raspberrypilearning/astro-pi-flight-case-mk2/en/images/all_4_spacers.jpg

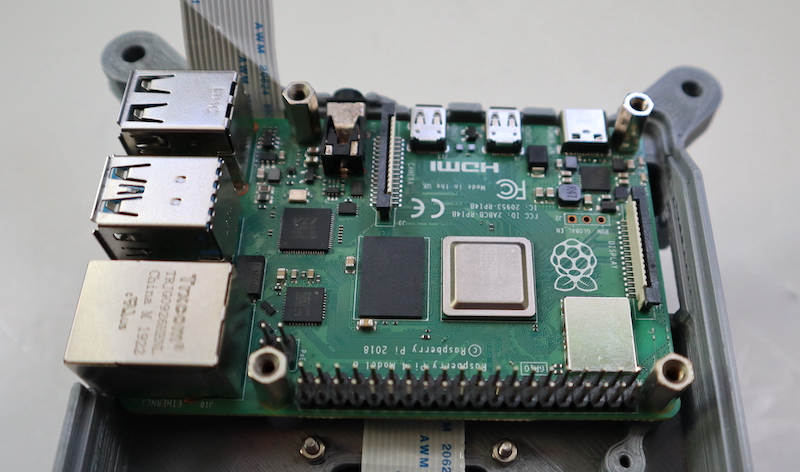
en/images/all_4_spacers.jpg
