raspberrypilearning/astro-pi-flight-case-mk2/en/images/both_panels.jpg

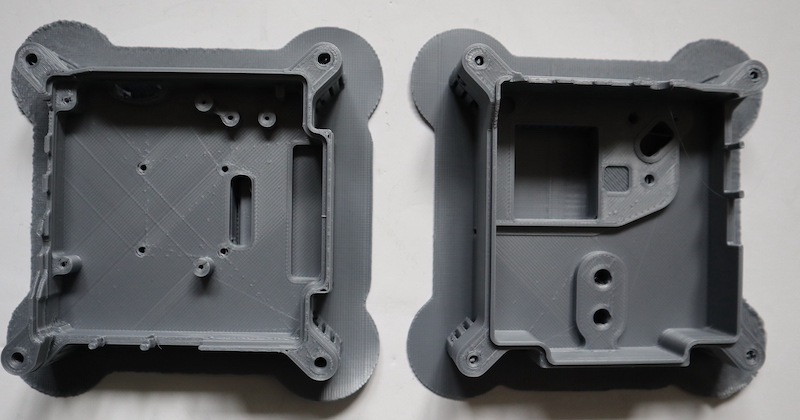
en/images/both_panels.jpg
