raspberrypilearning/astro-pi-flight-case-mk2/en/images/buttons_heatgun.JPG

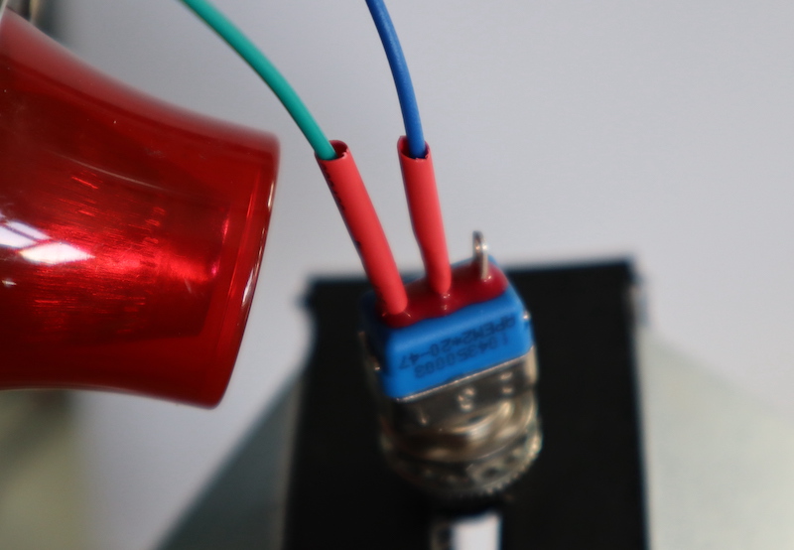
en/images/buttons_heatgun.JPG
