raspberrypilearning/astro-pi-flight-case-mk2/en/images/camera-slot-removed.jpg

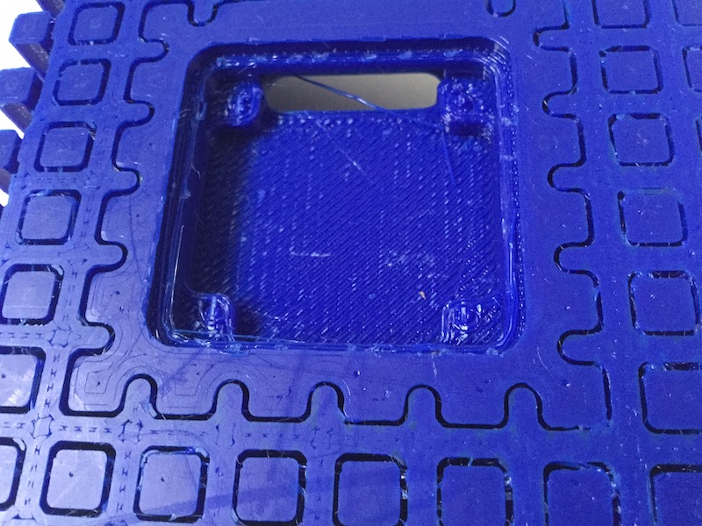
en/images/camera-slot-removed.jpg
