raspberrypilearning/astro-pi-flight-case-mk2/en/images/camera_mount_with_HQC_back.JPG

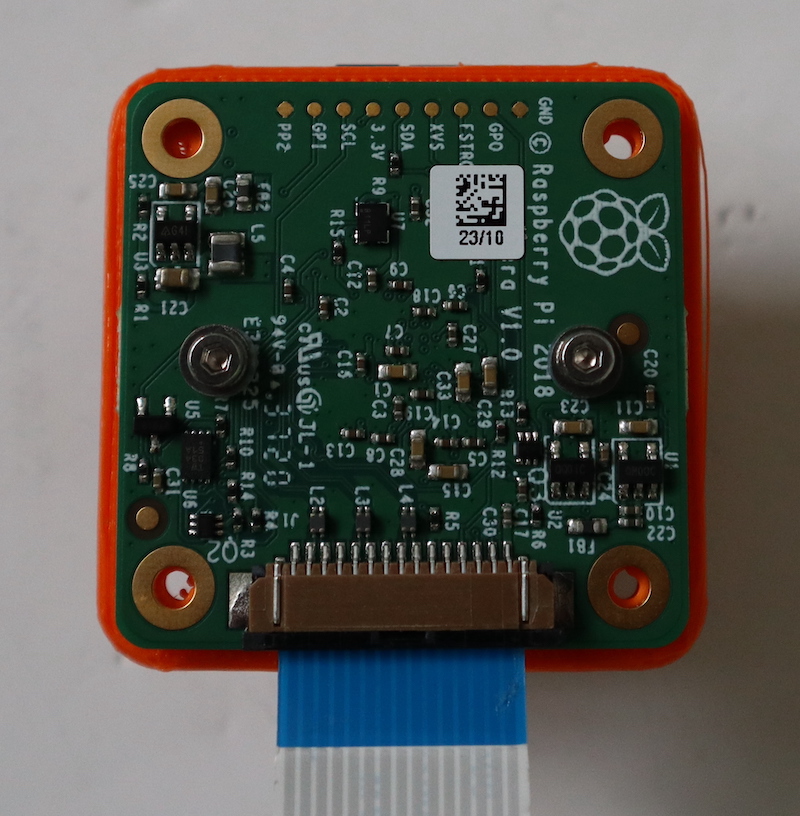
en/images/camera_mount_with_HQC_back.JPG
