raspberrypilearning/astro-pi-flight-case-mk2/en/images/completed_k.jpg

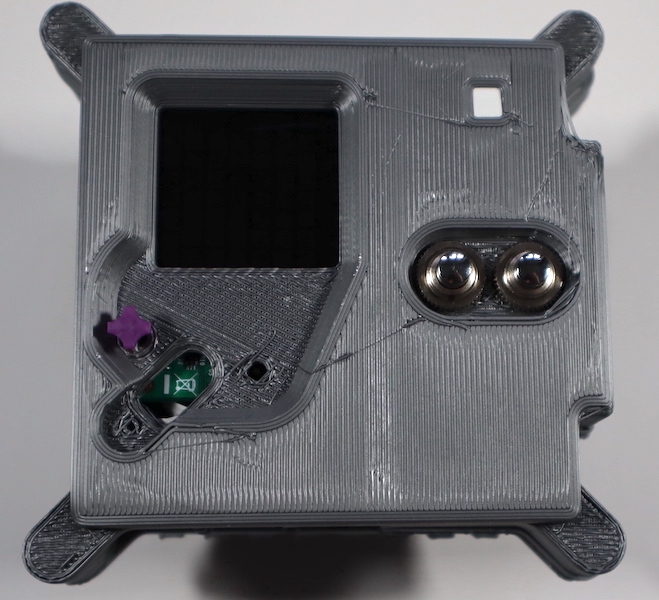
en/images/completed_k.jpg
