raspberrypilearning/astro-pi-flight-case-mk2/en/images/completed_p.jpg

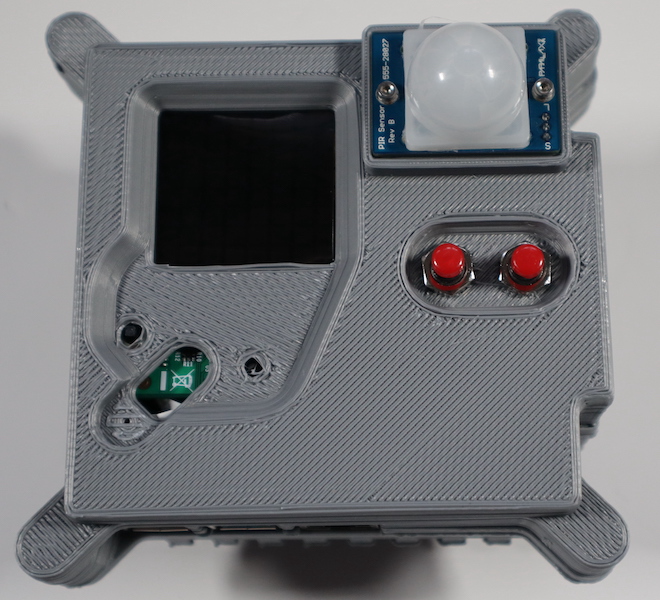
en/images/completed_p.jpg
