raspberrypilearning/astro-pi-flight-case-mk2/en/images/header_in_pi.jpg

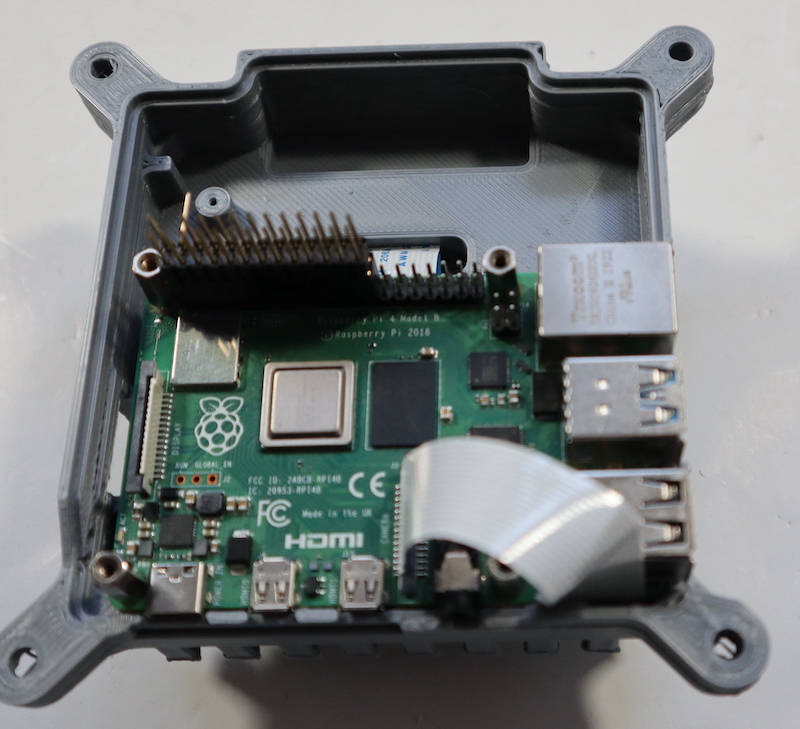
en/images/header_in_pi.jpg
