raspberrypilearning/astro-pi-flight-case-mk2/en/images/hedaer_bent_pin.jpg

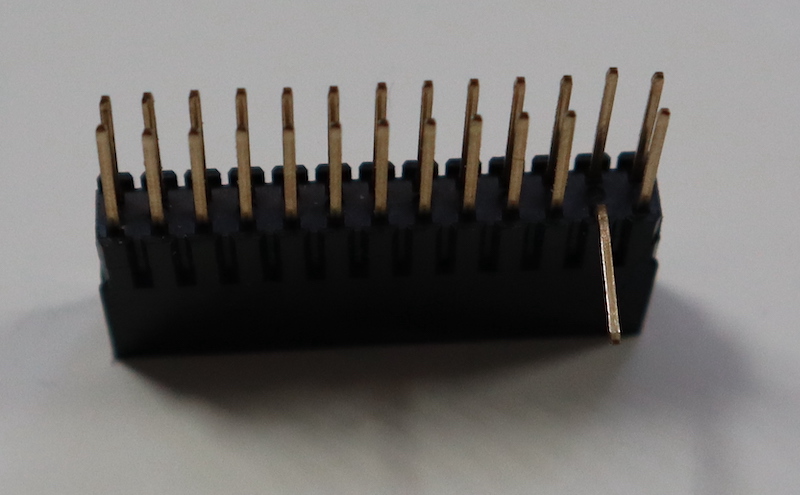
en/images/hedaer_bent_pin.jpg
