raspberrypilearning/astro-pi-flight-case-mk2/en/images/HQC_no_screws.jpg

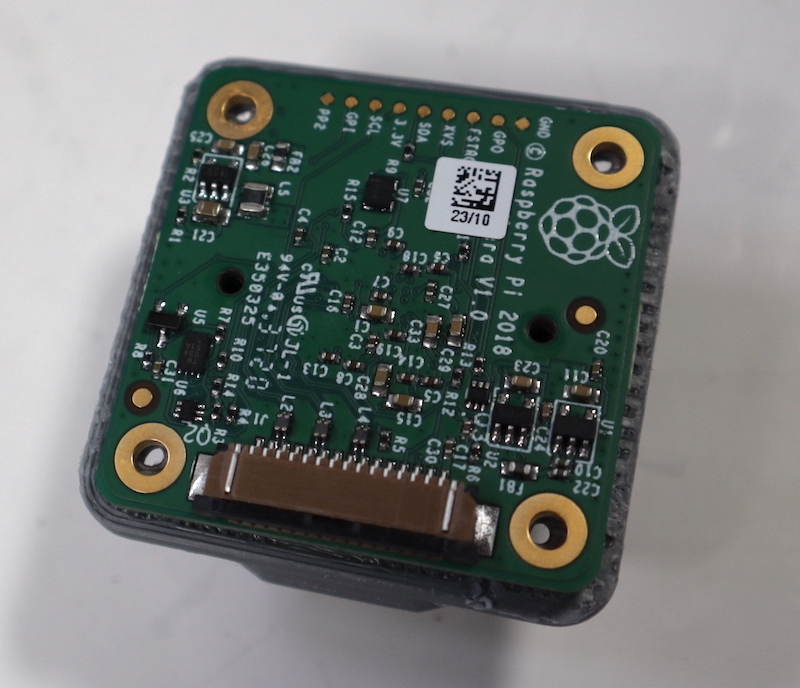
en/images/HQC_no_screws.jpg
