raspberrypilearning/astro-pi-flight-case-mk2/en/images/leg_scaff.jpg

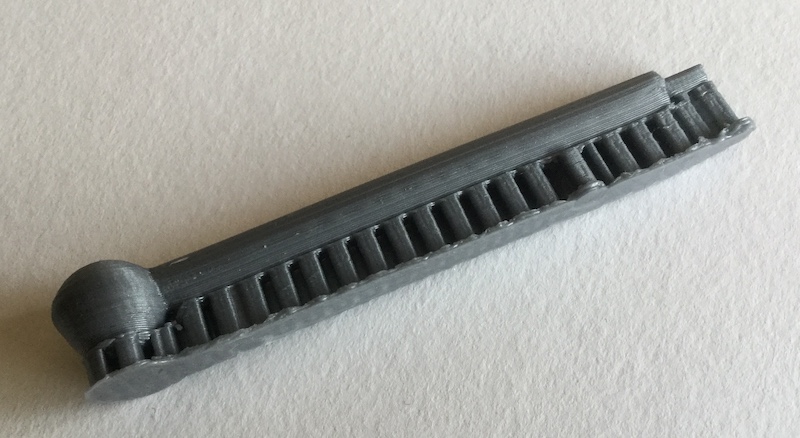
en/images/leg_scaff.jpg
