raspberrypilearning/astro-pi-flight-case-mk2/en/images/pi_added.JPG

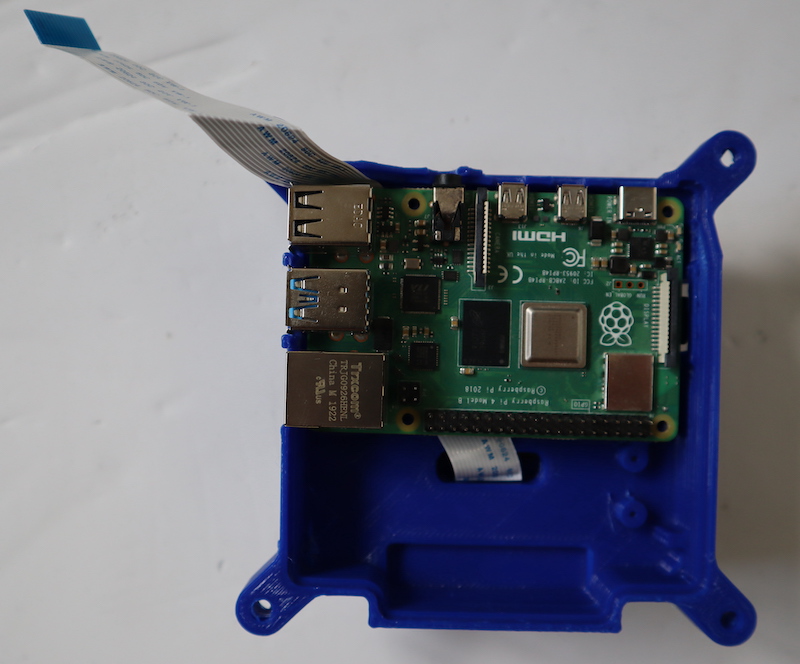
en/images/pi_added.JPG
