raspberrypilearning/astro-pi-flight-case-mk2/en/images/PIR_P_screws.jpg

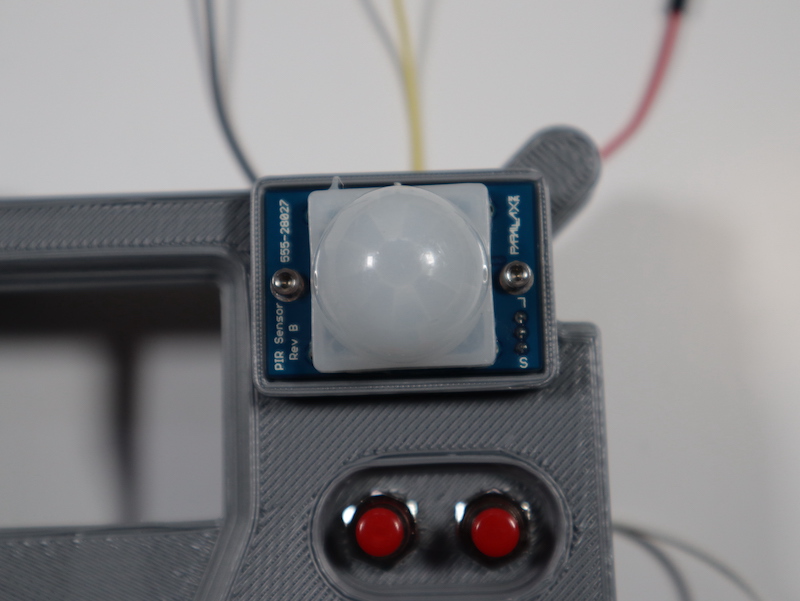
en/images/PIR_P_screws.jpg
